sourya-sen/N8IR-AV/Etc/IMG_3140.jpg

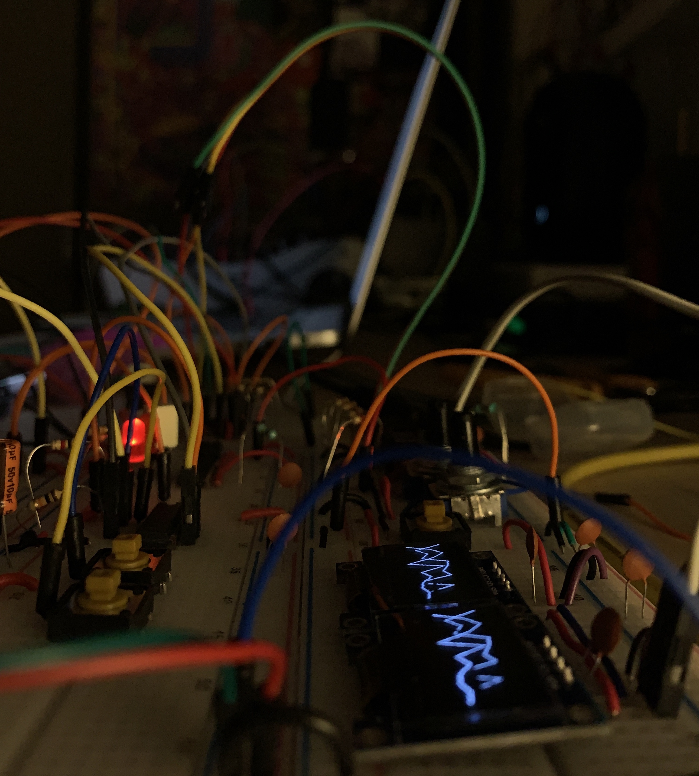
Etc/IMG_3140.jpg
